ferrance/corne_cases/upsidedown/lcd_1_3.stl

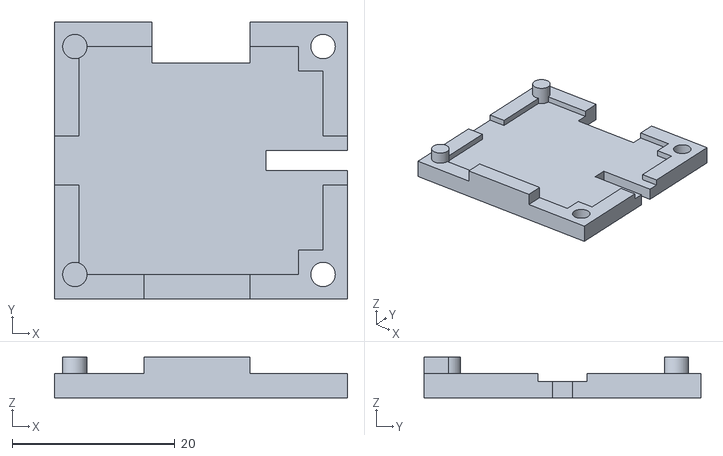
[picture p17: CAD file, 2023-05-31]
upsidedown/lcd_1_3.stl
36.0 x 34.0 x 5.00
