ferrance/corne_cases/stl/base_plate_round_20x5.stl

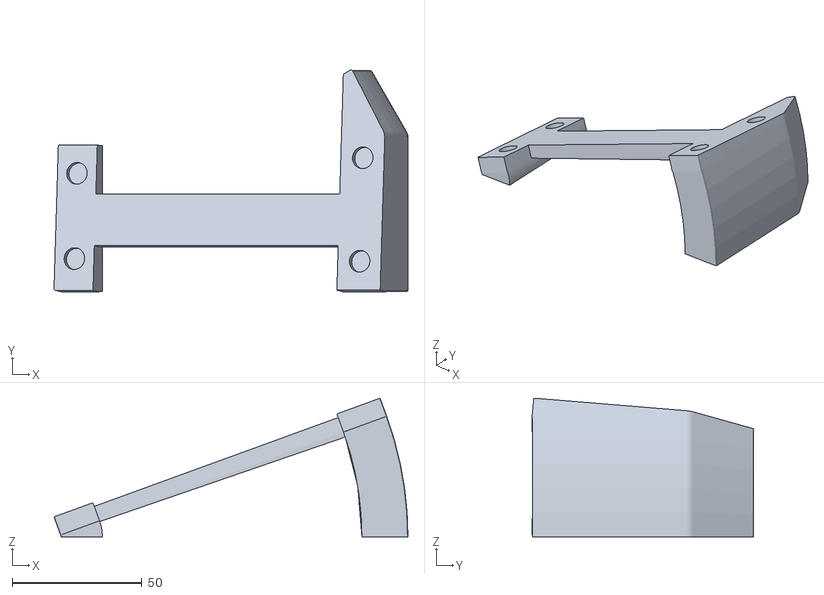
[picture p18: CAD file, 2023-09-30]
stl/base_plate_round_20x5.stl
136.4 x 85.5 x 53.4
