ferrance/corne_cases/stl/base_plate_round_25x5.stl

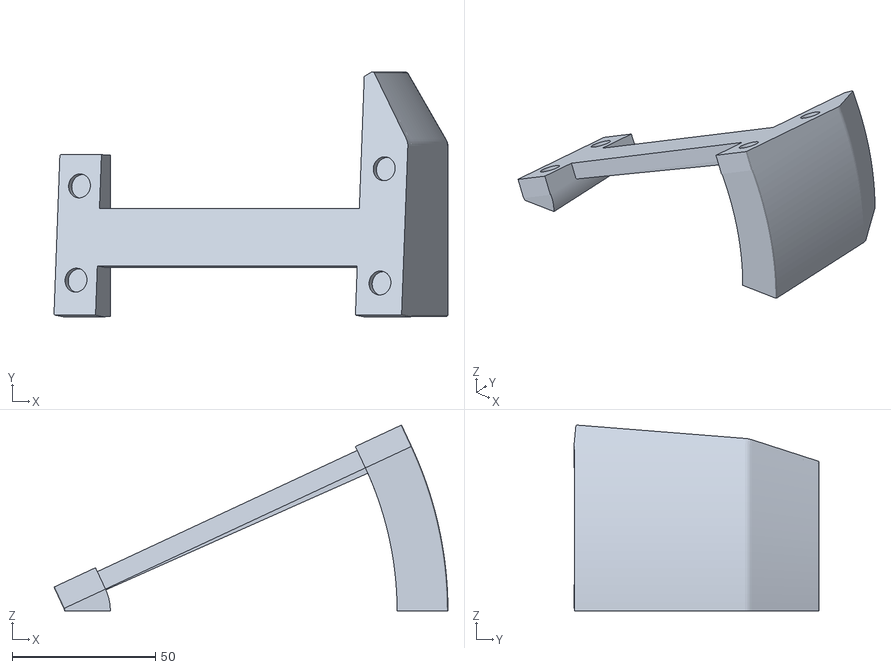
[picture p19: CAD file, 2023-09-30]
stl/base_plate_round_25x5.stl
137.4 x 85.6 x 64.8
