ferrance/corne_cases/stl/base_plate_5x5.stl

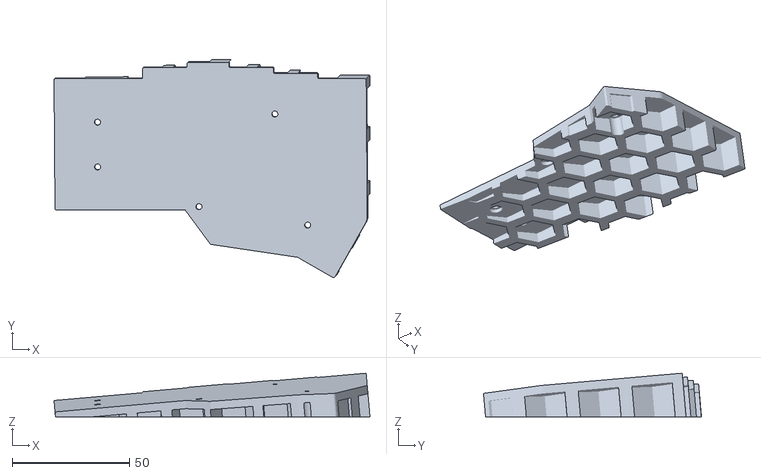
[picture p20: CAD file, 2023-05-13]
stl/base_plate_5x5.stl
134.9 x 93.1 x 18.6
