ferrance/corne_cases/stl/corne_feet.stl

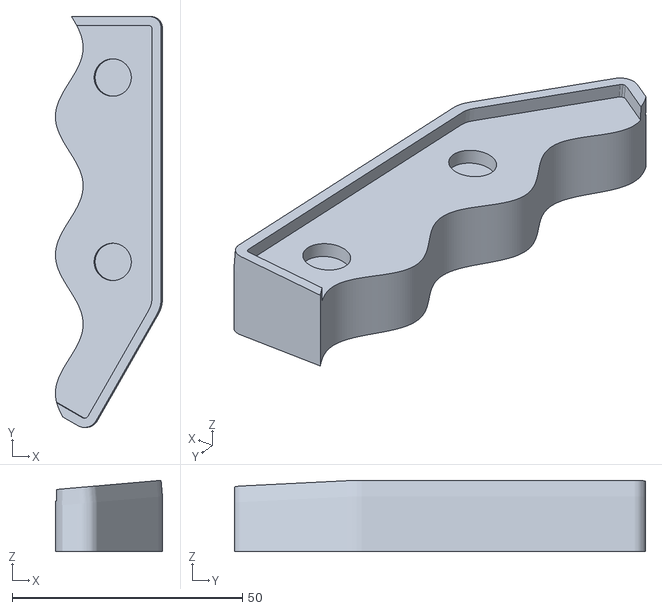
[picture p21: CAD file, 2023-05-02]
stl/corne_feet.stl
23.2 x 89.2 x 15.5
