ferrance/corne_cases/stl/one_piece.stl

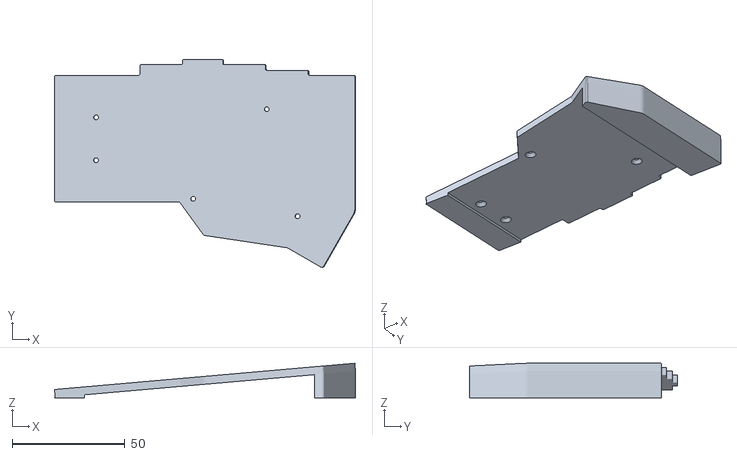
[picture p22: CAD file, 2023-05-02]
stl/one_piece.stl
133.6 x 92.2 x 15.3
