ferrance/corne_cases/stl/corne_flat_magnets.stl

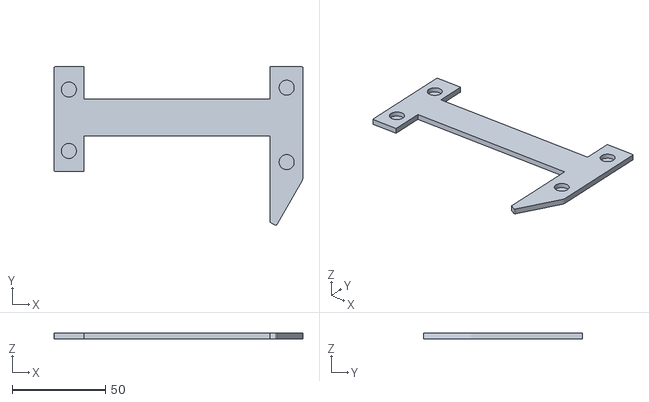
[picture p23: CAD file, 2023-05-02]
stl/corne_flat_magnets.stl
133.8 x 85.2 x 3.00
