ferrance/corne_cases/stl/corne_wedge_5x5.stl

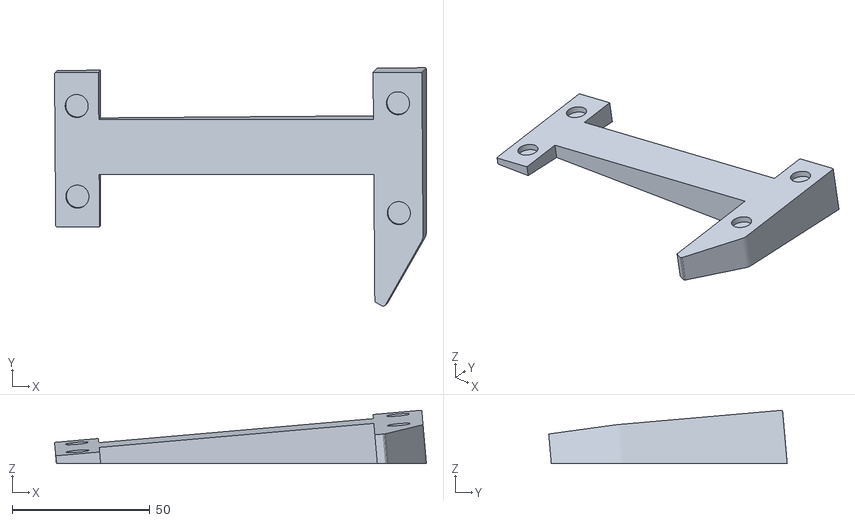
[picture p24: CAD file, 2023-05-02]
stl/corne_wedge_5x5.stl
134.9 x 86.6 x 19.4
